haarts/intercom/esp32-mumble/esphome/esp32-s3-box.yaml

---
# ESP32-S3-BOX (original Box, not Box-3) board config for Mumble client
# Uses ESP-IDF framework with lwIP netconn for UDP (BSD sockets have unicast UDP issues).
# Keep functionally in sync with esp32-s3-box3.yaml (same entities/features; only pins differ).
# Pinout: backlight GPIO45, I2S LRCLK GPIO47 (Box-3 uses backlight 47, LRCLK 45).
# Configure server, port, username, password, channel, and mode in Home Assistant UI (values persist in NVS)
# First flash after switching framework must be via USB, not OTA.

substitutions:
  name: esp32-mumble-box

esphome:
  name: ${name}
  name_add_mac_suffix: true
  min_version: "2026.7.0"
  project:
    name: dchote.esp32-mumble
    version: "dev"  # rewritten to the git tag by release.yml
  on_boot:
    - priority: 600
      then:
        - light.turn_on: screen_backlight
    - priority: -100
      then:
        - speaker.volume_set:
            id: box_speaker
            volume: !lambda |-
              float vol = id(mumble_speaker_volume).state;
              if (isnan(vol)) vol = 65;
              return vol / 100.0f;
  platformio_options:
    extra_scripts:
      - pre:../../../../scripts/patch_mbedtls_requires.py
    build_flags:
      - -Wno-cpp
      - -Wno-stringop-overread

esp32:
  board: esp32s3box
  flash_size: 16MB
  cpu_frequency: 240MHz
  # PlatformIO toolchain required for local symlink:// micro-opus and mbedtls pre-script.
  toolchain: platformio
  framework:
    type: esp-idf
    sdkconfig_options:
      CONFIG_ESP32S3_DEFAULT_CPU_FREQ_240: "y"
      CONFIG_ESP32S3_DATA_CACHE_64KB: "y"
      CONFIG_ESP32S3_DATA_CACHE_LINE_64B: "y"
      CONFIG_MBEDTLS_AES_C: "y"
      CONFIG_MBEDTLS_GCM_C: "y"
      CONFIG_ESP_TLS_INSECURE: "y"
      CONFIG_ESP_TLS_SKIP_SERVER_CERT_VERIFY: "y"

psram:
  mode: octal
  speed: 80MHz

wifi:
  networks:
    - ssid: !secret wifi_ssid
      password: !secret wifi_password

logger:
  hardware_uart: USB_SERIAL_JTAG

# Screen backlight: Box uses GPIO45 (Box-3 uses GPIO47). Default on for status display.
output:
  - platform: ledc
    pin:
      number: GPIO45
      ignore_strapping_warning: true
    id: backlight_output

light:
  - platform: monochromatic
    id: screen_backlight
    name: Screen
    icon: "mdi:television"
    entity_category: config
    output: backlight_output
    restore_mode: RESTORE_DEFAULT_ON

font:
  - file: "gfonts://Roboto"
    id: font_title
    size: 14
    glyphsets: [GF_Latin_Kernel]
  - file: "gfonts://Roboto"
    id: font_server
    size: 18
    glyphsets: [GF_Latin_Kernel]
  - file: "gfonts://Roboto Mono"
    id: font_small
    size: 14
    glyphsets: [GF_Latin_Kernel]

# SPI for display (Box: GPIO7 SCK, GPIO6 MOSI)
spi:
  - id: spi_bus
    clk_pin: GPIO7
    mosi_pin: GPIO6

# Display (required by touchscreen). Match wake-word-voice-assistants: S3BOX, invert_colors false, reset 48.
# Status display: active writes may help touchscreen; shows server, ping, mic/RX/TX, chat.
display:
  - platform: ili9xxx
    id: box_display
    model: S3BOX
    invert_colors: false
    data_rate: 40MHz
    spi_id: spi_bus
    cs_pin: 5
    dc_pin: 4
    reset_pin: 48
    update_interval: 1s
    lambda: |-
      int w = it.get_width();
      int h = it.get_height();
      auto fg = Color(255, 255, 255);
      auto dim = Color(140, 140, 140);
      auto bg = Color(24, 24, 28);
      auto card = Color(40, 40, 48);
      auto accent = Color(60, 60, 72);
      it.fill(bg);
      it.filled_rectangle(6, 6, w - 12, h - 12, card);
      it.rectangle(6, 6, w - 12, h - 12, accent);
      it.print(14, 10, id(font_title), dim, "ESP32-Mumble");
      auto srv = id(mumble_server_host).state;
      if (srv.empty()) srv = "--";
      else if (srv.length() > 22) srv = srv.substr(0, 19) + "...";
      it.print(14, 30, id(font_small), fg, srv.c_str());
      float p = id(mumble_ping_sensor).state;
      if (isnan(p)) it.print(w - 14, 30, id(font_small), dim, TextAlign::TOP_RIGHT, "Ping: --");
      else it.printf(w - 14, 30, id(font_small), fg, TextAlign::TOP_RIGHT, "Ping: %.0f ms", p);
      it.horizontal_line(14, 51, w - 28);
      bool muted = id(button_microphone).state;
      bool rx = id(mumble_voice_active).state;
      bool tx = id(mumble_voice_sending).state;
      it.printf(14, 55, id(font_small), muted ? Color(240, 100, 100) : dim, "Mic: %s", muted ? "MUTED" : "UNMUTED");
      it.printf(w / 2, 55, id(font_small), rx ? Color(100, 220, 120) : dim, TextAlign::TOP_CENTER, "RX: %s", rx ? "on" : "off");
      it.printf(w - 14, 55, id(font_small), tx ? Color(100, 180, 255) : dim, TextAlign::TOP_RIGHT, "TX: %s", tx ? "on" : "off");
      it.horizontal_line(14, 76, w - 28);
      const int chat_y0 = 80;
      const int line_height = 16;
      const int max_chat_lines = (h - 12 - chat_y0) / line_height;
      const int max_chars = 34;
      const auto &msgs = id(mumble_client).get_chat_messages();
      size_t start = msgs.size() > (size_t) max_chat_lines ? msgs.size() - max_chat_lines : 0;
      int y = chat_y0;
      for (size_t i = start; i < msgs.size() && y + line_height <= h - 6; i++) {
        std::string line = msgs[i].sender + ": " + msgs[i].message;
        if (line.length() > (size_t) max_chars) line = line.substr(0, max_chars - 3) + "...";
        it.print(14, y, id(font_small), fg, line.c_str());
        y += line_height;
      }

# Touchscreen: original Box uses TT21100 (Box-3 uses GT911). Red circle button is index 0.
# Omit reset_pin — shared with display; display init performs reset.
# Use polling (update_interval) instead of interrupt; interrupt can fail on some hardware.
touchscreen:
  - platform: tt21100
    id: box_touchscreen
    display: box_display
    update_interval: 50ms

# GPIO1 = hardware mic mute button (latching toggle). LED off = unmuted, LED on = muted.
# On unmute, re-init ES7210 via I2C to restore ADC registers after hardware mute.
binary_sensor:
  - platform: tt21100
    name: "PTT"
    id: button_ptt
    tt21100_id: box_touchscreen
    index: 0
    on_press:
      - if:
          condition:
            - binary_sensor.is_on: mumble_connected_sensor
          then:
            - if:
                condition:
                  - lambda: 'return id(mumble_client).get_mode() == 2;'
                then:
                  - mumble.communicator_toggle: mumble_client
                else:
                  - mumble.microphone_enable: mumble_client
    on_release:
      - if:
          condition:
            - lambda: 'return id(mumble_client).get_mode() != 2;'
          then:
            - mumble.microphone_disable: mumble_client
  - platform: gpio
    pin:
      number: GPIO1
      mode: INPUT_PULLUP
      inverted: true
    name: "Microphone Muted"
    id: button_microphone
    on_state:
      - if:
          condition:
            binary_sensor.is_on: button_microphone
          then:
            - microphone.mute:
            - mumble.microphone_disable: mumble_client
          else:
            - lambda: id(es7210_adc).setup();
            - delay: 50ms
            - microphone.unmute:
            - mumble.microphone_enable: mumble_client
  - platform: template
    name: "Voice Received"
    id: mumble_voice_active
    icon: "mdi:microphone-message"
    device_class: running
    lambda: |-
      return id(mumble_client).get_voice_active();
  - platform: template
    name: "Voice Sending"
    id: mumble_voice_sending
    icon: "mdi:microphone"
    device_class: running
    lambda: |-
      return id(mumble_client).get_voice_sending();
# Diagnostics
  - platform: template
    name: "Mumble Connected"
    id: mumble_connected_sensor
    icon: "mdi:connection"
    entity_category: diagnostic
    device_class: connectivity
    lambda: |-
      return id(mumble_client).is_connected();
# Box I2S: LRCLK=47, BCLK=17, MCLK=2 (Box-3 uses LRCLK=45)
i2c:
  scl: GPIO18
  sda: GPIO8

i2s_audio:
  - id: i2s_audio_bus
    i2s_lrclk_pin: GPIO47
    i2s_bclk_pin: GPIO17
    i2s_mclk_pin: GPIO2

audio_adc:
  - platform: es7210
    id: es7210_adc
    bits_per_sample: 16bit
    sample_rate: 16000
    mic_gain: 30dB

audio_dac:
  - platform: es8311
    id: es8311_dac
    bits_per_sample: 16bit
    sample_rate: 16000

microphone:
  - platform: i2s_audio
    id: box_mic
    sample_rate: 16000
    i2s_din_pin: GPIO16
    i2s_audio_id: i2s_audio_bus
    bits_per_sample: 16bit
    channel: left
    adc_type: external
    correct_dc_offset: true

speaker:
  - platform: i2s_audio
    id: box_speaker
    i2s_dout_pin: GPIO15
    dac_type: external
    sample_rate: 16000
    bits_per_sample: 16bit
    channel: left
    audio_dac: es8311_dac
    buffer_duration: 500ms

# Communicator chime: embedded in Mumble component (bus-aware playback via manage_i2s_bus)

api:
  # Optional: encryption: { key: !secret api_encryption_key }
  on_client_connected:
    - lambda: |-
        if (id(mumble_server_host).state.empty()) {
          ESP_LOGI("mumble", "Server not configured; using Home Assistant IP: %s", client_address.c_str());
          id(mumble_server_host).make_call().set_value(client_address).perform();
        }

# Managed OTA from GitHub Pages manifests (see docs/features/0015-ota-releases.md).
# verify_ssl false matches the project's trusted-LAN TLS posture.
http_request:
  verify_ssl: false

ota:
  - platform: esphome
    # Optional: password: !secret ota_password
  - platform: http_request

update:
  - platform: http_request
    name: "Firmware Update"
    id: firmware_update
    update_interval: 6h
    source: https://dchote.github.io/esp32-mumble/esp32-s3-box/manifest.json

# Mumble connection and mode settings (Configuration section; persisted to NVS)
# Entity names use numeric prefixes for display order: server, port, username, password, channel, mode
# Port is text (not number) so it displays as integer in HA, per home-assistant-voice-pe pattern
text:
  - platform: template
    id: mumble_server_host
    name: "1. Server"
    icon: "mdi:server-network"
    entity_category: config
    mode: text
    optimistic: true
    restore_value: true
    initial_value: ""
    max_length: 253
  - platform: template
    id: mumble_server_port
    name: "2. Port"
    icon: "mdi:ethernet"
    entity_category: config
    mode: text
    optimistic: true
    restore_value: true
    initial_value: "64738"
    max_length: 5
  - platform: template
    id: mumble_username
    name: "3. Username"
    icon: "mdi:account"
    entity_category: config
    mode: text
    optimistic: true
    restore_value: true
    initial_value: ""  # Seeded with esp32-<MAC> at setup; user can overwrite
    max_length: 128
  - platform: template
    id: mumble_password
    name: "4. Password"
    icon: "mdi:key"
    entity_category: config
    mode: password
    optimistic: true
    restore_value: true
    initial_value: ""  # Component publishes empty default at setup (avoids HA "unknown")
    max_length: 128
  - platform: template
    id: mumble_channel
    name: "5. Channel"
    icon: "mdi:forum"
    entity_category: config
    mode: text
    optimistic: true
    restore_value: true
    initial_value: "Root"  # Default channel; case-insensitive match
    max_length: 128
select:
  - platform: template
    id: mumble_mode
    name: "6. Mode"
    icon: "mdi:microphone-settings"
    entity_category: config
    optimistic: true
    restore_value: true
    initial_option: "always_on"
    options:
      - "always_on"
      - "push_to_talk"
      - "communicator"
  - platform: template
    id: mumble_crypto
    name: "7. Crypto"
    icon: "mdi:lock"
    entity_category: config
    optimistic: true
    restore_value: true
    initial_option: "legacy"
    options:
      - "legacy"
      - "lite"

# Diagnostics section (HA device page)
button:
  - platform: template
    name: "Reset Config"
    id: mumble_reset_config
    icon: "mdi:restore"
    entity_category: diagnostic
    on_press:
      - mumble.reset_config: mumble_client
      - number.set:
          id: mumble_speaker_volume
          value: 65
  - platform: restart
    name: "Reboot"
    id: mumble_reboot
    icon: "mdi:restart"
    entity_category: diagnostic
text_sensor:
  - platform: template
    name: "Transport"
    id: mumble_transport
    icon: "mdi:protocol"
    entity_category: diagnostic
    lambda: |-
      if (id(mumble_client).get_voice_transport_udp()) {
        return {"UDP"};
      } else {
        return {"TCP"};
      }
    update_interval: 5s
sensor:
  - platform: wifi_signal
    name: "WiFi Signal"
    icon: "mdi:wifi"
    entity_category: diagnostic
    update_interval: 60s
  - platform: template
    name: "Mumble Ping"
    id: mumble_ping_sensor
    icon: "mdi:lan"
    entity_category: diagnostic
    unit_of_measurement: "ms"
    device_class: duration
    accuracy_decimals: 0
    lambda: |-
      return id(mumble_client).get_ping_ms();
    update_interval: 5s

# Controls: speaker volume and microphone
number:
  - platform: template
    name: "Speaker Volume"
    id: mumble_speaker_volume
    icon: "mdi:volume-high"
    entity_category: config
    optimistic: true
    restore_value: true
    min_value: 0
    max_value: 100
    step: 5
    initial_value: 65
    set_action:
      - speaker.volume_set:
          id: box_speaker
          volume: !lambda 'return x / 100.0;'

# Speaker Enable: Box-3 uses GPIO46; original Box may use same PA pin (disable if not present)
switch:
  - platform: gpio
    name: "Speaker Power"
    icon: "mdi:speaker"
    pin:
      number: GPIO46
      ignore_strapping_warning: true
    restore_mode: RESTORE_DEFAULT_ON
    entity_category: config
  - platform: template
    name: "Mute"
    id: mute
    icon: "mdi:microphone-off"
    optimistic: true
    restore_mode: RESTORE_DEFAULT_OFF
    entity_category: config
    on_turn_on:
      - microphone.mute:
      - mumble.microphone_disable: mumble_client
    on_turn_off:
      - microphone.unmute:
      - mumble.microphone_enable: mumble_client

external_components:
  - source:
      type: local
      path: ../components

mumble:
  id: mumble_client
  server: ""  # Empty by default; auto-filled from HA IP when adopted, or set manually
  port: 64738
  username: ""
  password: ""
  channel: "Root"
  server_text_id: mumble_server_host
  port_text_id: mumble_server_port
  username_text_id: mumble_username
  password_text_id: mumble_password
  channel_text_id: mumble_channel
  mode_select_id: mumble_mode
  crypto_select_id: mumble_crypto
  microphone_id: box_mic
  speaker_id: box_speaker
  mode: always_on
  crypto: legacy
  # Optional: set ca_cert to a PEM CA string to verify the Mumble server TLS cert (default: insecure, trusted LAN).
  # mute_pin: GPIO38  # Hardware mute switch if available
