haarts/intercom/esp32-mumble/components/mumble/mumble_client.h

#pragma once

#include "mumble_messages.h"
#include "mumble_permissions.h"
#include "mumble_protocol.h"
#include "mumble_socket.h"
#include <cstdint>
#include <functional>
#include <map>
#include <string>
#include <vector>

namespace esphome {
namespace mumble {

struct ChannelInfo {
  uint32_t id = 0;
  uint32_t parent_id = 0;
  std::string name;
  bool temporary = false;
  int32_t position = 0;
};

struct UserInfo {
  uint32_t session = 0;
  std::string name;
  uint32_t channel_id = 0;
  bool mute = false;
  bool deaf = false;
  bool self_mute = false;
  bool self_deaf = false;
};

enum class ConnectionState {
  DISCONNECTED,
  CONNECTING,
  AUTHENTICATING,
  CONNECTED,
};

class MumbleClient {
public:
  MumbleClient() = default;
  ~MumbleClient() {
    if (tls_client_ != nullptr) {
      mumble_free_tls_client(tls_client_);
      tls_client_ = nullptr;
    }
  }

  void set_server(const std::string &server) { server_ = server; }
  void set_port(uint16_t port) { port_ = port; }
  void set_username(const std::string &username) { username_ = username; }
  void set_password(const std::string &password) { password_ = password; }
  void set_channel(const std::string &channel) { channel_ = channel; }
  void set_crypto(uint8_t crypto) { crypto_mode_ = crypto; }
  /** Optional: PEM of CA cert for server verification. When set, setInsecure() is not used. */
  void set_ca_cert(const std::string &pem) { ca_cert_ = pem; }
  /** When true, send client_type=1 (bot) in Authenticate so server can treat this as a bot. */
  void set_bot_mode(bool bot) { bot_mode_ = bot; }

  bool connect();
  void disconnect();
  bool is_connected() const { return state_ == ConnectionState::CONNECTED; }
  void loop();

  float get_ping_rtt_ms() const { return ping_rtt_ms_; }
  uint32_t get_session_id() const { return session_id_; }
  /** Peer IP (network byte order) from TLS connection; 0 if not connected. Use for UDP to avoid DNS/IP mismatch. */
  uint32_t get_peer_ip() const { return (tls_client_ != nullptr && is_connected()) ? tls_client_->get_peer_ip() : 0; }

  bool has_crypt_setup() const { return crypt_setup_received_; }
  const std::vector<uint8_t> &get_crypt_key() const { return crypt_key_; }
  const std::vector<uint8_t> &get_crypt_client_nonce() const { return crypt_client_nonce_; }
  const std::vector<uint8_t> &get_crypt_server_nonce() const { return crypt_server_nonce_; }
  /** 0 = lite, 1 = legacy (OCB2), 2 = secure (GCM). Only valid after CryptSetup. */
  uint8_t get_crypt_negotiated_mode() const { return crypt_negotiated_mode_; }
  void clear_crypt_setup() {
    crypt_setup_received_ = false;
    crypt_negotiated_mode_ = 0;
  }
  const std::vector<ChannelInfo> &get_channels() const { return channels_; }
  const std::vector<UserInfo> &get_users() const { return users_; }
  uint32_t find_channel_by_name(const std::string &name) const;
  void join_channel_by_id(uint32_t channel_id);
  uint32_t get_current_channel_id() const; // Our user's channel, or 0 if unknown
  // Build channel options for select: "id:Name" (flat list). Fills out_strings and out_ids.
  void build_channel_tree_options(std::vector<std::string> &out_strings, std::vector<uint32_t> &out_ids) const;

  // Send CryptSetup with only client_nonce to trigger server nonce resync
  void send_crypt_resync(const uint8_t *encrypt_iv, size_t len);

  /** Set UDP/crypto stats for next Ping message (good, late, lost, resync, udp_packets). */
  void set_udp_stats(uint32_t good, uint32_t late, uint32_t lost, uint32_t resync, uint32_t udp_packets) {
    ping_udp_good_ = good;
    ping_udp_late_ = late;
    ping_udp_lost_ = lost;
    ping_udp_resync_ = resync;
    ping_udp_packets_ = udp_packets;
  }

  using VoicePacketCallback = std::function<void(const uint8_t *data, size_t len)>;
  void set_voice_packet_callback(VoicePacketCallback cb) { voice_packet_callback_ = std::move(cb); }

  // Typed event callbacks (optional; fired after internal state update)
  using TextMessageCallback = std::function<void(const MsgTextMessage &)>;
  void set_text_message_callback(TextMessageCallback cb) { text_message_callback_ = std::move(cb); }
  using PermissionDeniedCallback = std::function<void(const MsgPermissionDenied &)>;
  void set_permission_denied_callback(PermissionDeniedCallback cb) { permission_denied_callback_ = std::move(cb); }
  using ChannelStateCallback = std::function<void(const MsgChannelState &)>;
  void set_channel_state_callback(ChannelStateCallback cb) { channel_state_callback_ = std::move(cb); }
  using ChannelRemoveCallback = std::function<void(uint32_t channel_id)>;
  void set_channel_remove_callback(ChannelRemoveCallback cb) { channel_remove_callback_ = std::move(cb); }
  using UserStateCallback = std::function<void(const MsgUserState &)>;
  void set_user_state_callback(UserStateCallback cb) { user_state_callback_ = std::move(cb); }
  using UserRemoveCallback = std::function<void(const MsgUserRemove &)>;
  void set_user_remove_callback(UserRemoveCallback cb) { user_remove_callback_ = std::move(cb); }
  using RawMessageCallback = std::function<void(uint16_t msg_type, const uint8_t *payload, size_t len)>;
  void set_raw_message_callback(RawMessageCallback cb) { raw_message_callback_ = std::move(cb); }

  /** Send voice packet via TCP UDPTunnel (message type 1). Used when UDP is not active. */
  bool send_udp_tunnel(const uint8_t *data, size_t len);

  /** Send text message to a channel (channel_id 0 = root). */
  bool send_text_message(const std::string &message, uint32_t channel_id);
  /** Send text message to specific user sessions. */
  bool send_text_message(const std::string &message, const std::vector<uint32_t> &sessions);
  /** Send text message to channel subtree (all users in channel and subchannels). */
  bool send_tree_message(const std::string &message, uint32_t channel_id);

  /** Set self-mute state (send UserState with self_mute). */
  bool send_self_mute(bool mute);
  /** Set self-deaf state (send UserState with self_deaf). */
  bool send_self_deaf(bool deaf);
  /** Set own comment (send UserState with comment). */
  bool send_user_comment(const std::string &comment);
  /** Kick user by session (send UserRemove with session, reason, actor=our session). */
  bool send_kick(uint32_t session, const std::string &reason);
  /** Ban and kick user (send UserRemove with session, reason, actor, ban=true). */
  bool send_ban(uint32_t session, const std::string &reason);
  /** Request ban list from server (send BanList with query=true). */
  bool send_ban_list_query();
  /** Send QueryUsers to resolve ids to names and/or names to ids. */
  bool send_query_users(const std::vector<uint32_t> &ids, const std::vector<std::string> &names);
  /** Request UserStats for a session. */
  bool send_user_stats(uint32_t session, bool stats_only = false);

  /** Request effective permissions for a channel (server responds with PermissionQuery). */
  bool send_permission_query(uint32_t channel_id);
  /** Request ACL for a channel (server responds with ACL message). */
  bool send_acl_query(uint32_t channel_id);
  /** Check cached permission for channel (returns false if not in cache). */
  bool has_permission(uint32_t channel_id, uint32_t permission) const;

  /** Create a new channel (channel_id=0, parent_id, name, temporary). */
  bool send_create_channel(uint32_t parent_id, const std::string &name, bool temporary = false);
  /** Update channel. Pass nullptr/empty for name to skip; position INT32_MIN to skip; max_users UINT32_MAX to skip. */
  bool send_edit_channel(uint32_t channel_id, const std::string *name = nullptr, int32_t position = INT32_MIN,
                         uint32_t max_users = UINT32_MAX);
  /** Remove a channel (send ChannelRemove). */
  bool send_remove_channel(uint32_t channel_id);
  /** Set channel links (send ChannelState with channel_id and links list). */
  bool send_channel_links(uint32_t channel_id, const std::vector<uint32_t> &links);

  /** Register a voice target with the server (id 1-30). Targets: sessions and/or channel+options. */
  bool send_voice_target(uint8_t id, const std::vector<MsgVoiceTargetTarget> &targets);

  /** Request blobs (textures, comments, channel descriptions) by session/channel ids. */
  bool send_request_blob(const std::vector<uint32_t> &session_texture, const std::vector<uint32_t> &session_comment,
                         const std::vector<uint32_t> &channel_description);
  /** Trigger a context action (plugin-defined). */
  bool send_context_action(uint32_t session, uint32_t channel_id, const std::string &action);
  /** Send plugin data to specific sessions. */
  bool send_plugin_data(const std::string &data_id, const std::vector<uint8_t> &data,
                        const std::vector<uint32_t> &receiver_sessions);

private:
  bool write_all(const uint8_t *buf, size_t len);
  bool send_message(uint16_t type, const uint8_t *payload, size_t payload_len);
  void handle_message(uint16_t type, const uint8_t *payload, size_t len);
  void send_version();
  void send_authenticate();
  void send_ping();
  void join_channel(const std::string &name);

  void on_version(const uint8_t *payload, size_t len);
  void on_crypt_setup(const uint8_t *payload, size_t len);
  void on_channel_state(const uint8_t *payload, size_t len);
  void on_channel_remove(const uint8_t *payload, size_t len);
  void on_user_state(const uint8_t *payload, size_t len);
  void on_user_remove(const uint8_t *payload, size_t len);
  void on_server_sync(const uint8_t *payload, size_t len);
  void on_ping(const uint8_t *payload, size_t len);
  void on_reject(const uint8_t *payload, size_t len);
  void on_codec_version(const uint8_t *payload, size_t len);
  void on_server_config(const uint8_t *payload, size_t len);
  void on_udp_tunnel(const uint8_t *payload, size_t len);
  void on_ban_list(const uint8_t *payload, size_t len);
  void on_text_message(const uint8_t *payload, size_t len);
  void on_permission_denied(const uint8_t *payload, size_t len);
  void on_acl(const uint8_t *payload, size_t len);
  void on_query_users(const uint8_t *payload, size_t len);
  void on_context_action_modify(const uint8_t *payload, size_t len);
  void on_context_action(const uint8_t *payload, size_t len);
  void on_user_list(const uint8_t *payload, size_t len);
  void on_voice_target(const uint8_t *payload, size_t len);
  void on_user_stats(const uint8_t *payload, size_t len);
  void on_request_blob(const uint8_t *payload, size_t len);
  void on_suggest_config(const uint8_t *payload, size_t len);
  void on_plugin_data_transmission(const uint8_t *payload, size_t len);
  void on_permission_query(const uint8_t *payload, size_t len);

  void update_channel(const MsgChannelState &m);
  void remove_channel(uint32_t id);
  void update_user(const MsgUserState &m);
  void remove_user(uint32_t session);

  std::string server_;
  uint16_t port_{64738};
  std::string username_;
  std::string password_;
  std::string channel_;
  uint8_t crypto_mode_{0};
  std::string ca_cert_;
  bool bot_mode_{false};

  // Crypto material from CryptSetup (stored until crypt state is initialized)
  std::vector<uint8_t> crypt_key_;
  std::vector<uint8_t> crypt_client_nonce_;
  std::vector<uint8_t> crypt_server_nonce_;
  bool crypt_setup_received_{false};
  uint8_t crypt_negotiated_mode_{0}; // 0=lite, 1=legacy, 2=secure
  bool unknown_crypt_logged_{false};

  TlsClient *tls_client_{nullptr};
  std::vector<uint8_t> recv_buf_;
  static constexpr size_t RECV_BUF_MAX = 16384;
  static constexpr size_t MAX_PAYLOAD_PRACTICAL = 16384;

  ConnectionState state_{ConnectionState::DISCONNECTED};
  uint32_t session_id_{0};
  uint32_t max_bandwidth_{0};
  std::string welcome_text_;
  std::vector<ChannelInfo> channels_;
  std::vector<UserInfo> users_;
  static constexpr size_t MAX_CHANNELS = 128;
  static constexpr size_t MAX_USERS = 128;

  uint32_t last_ping_ms_{0};
  uint64_t last_ping_timestamp_{0};
  float ping_rtt_ms_{0};
  uint32_t ping_udp_good_{0};
  uint32_t ping_udp_late_{0};
  uint32_t ping_udp_lost_{0};
  uint32_t ping_udp_resync_{0};
  uint32_t ping_udp_packets_{0};
  static constexpr uint32_t PING_INTERVAL_MS = 15000;
  static constexpr uint32_t PING_TIMEOUT_MS = 45000;

  uint32_t reconnect_delay_ms_{1000};
  uint32_t last_connect_attempt_ms_{0};
  uint32_t network_connected_since_ms_{0}; // 0 = disconnected or not yet tracked
  uint32_t reject_count_{0};               // Consecutive rejections; stop after max
  static constexpr uint32_t RECONNECT_DELAY_MAX_MS = 30000;
  static constexpr uint32_t MAX_REJECT_ATTEMPTS = 5;
  static constexpr uint32_t CONNECT_TIMEOUT_MS = 10000;
  static constexpr uint32_t WIFI_STABILITY_DELAY_MS = 5000; // Wait after WiFi before Mumble connect
  bool channel_join_sent_{false};
  std::map<uint32_t, uint32_t> permission_cache_; // channel_id -> effective permissions
  VoicePacketCallback voice_packet_callback_;
  TextMessageCallback text_message_callback_;
  PermissionDeniedCallback permission_denied_callback_;
  ChannelStateCallback channel_state_callback_;
  ChannelRemoveCallback channel_remove_callback_;
  UserStateCallback user_state_callback_;
  UserRemoveCallback user_remove_callback_;
  RawMessageCallback raw_message_callback_;
};

} // namespace mumble
} // namespace esphome
