haarts/intercom/esp32-mumble/components/mumble/mumble_diag.h

#pragma once

#include <cstddef>
#include <cstdint>

namespace esphome {
namespace mumble {

/** Run once at boot: diagnose byte-order, IP format, and sockaddr patterns.
 *  Only active when USE_ESP_IDF is defined (ESP-IDF framework builds). */
void mumble_diag_run_boot();

/** Log up to max_bytes of data as hex. Tag used for ESP_LOG*. */
void mumble_log_hex(const char *tag, const char *prefix, const uint8_t *data, size_t len, size_t max_bytes = 32);

} // namespace mumble
} // namespace esphome
